SLawson/PMODIO/src/function_test/pmodio_function_test.xdc

## Constraints file for the PMODIO Function Test
## 

## Clock signal
set_property -dict { PACKAGE_PIN E3    IOSTANDARD LVCMOS33 } [get_ports { clk }]; #IO_L12P_T1_MRCC_35 Sch=clk100mhz
create_clock -add -name sys_clk_pin -period 10.00 -waveform {0 5} [get_ports {clk}];

## LEDs

set_property -dict { PACKAGE_PIN H17   IOSTANDARD LVCMOS33 } [get_ports { led[0] }]; #IO_L18P_T2_A24_15 Sch=led[0]
set_property -dict { PACKAGE_PIN K15   IOSTANDARD LVCMOS33 } [get_ports { led[1] }]; #IO_L24P_T3_RS1_15 Sch=led[1]
set_property -dict { PACKAGE_PIN J13   IOSTANDARD LVCMOS33 } [get_ports { led[2] }]; #IO_L17N_T2_A25_15 Sch=led[2]
set_property -dict { PACKAGE_PIN N14   IOSTANDARD LVCMOS33 } [get_ports { led[3] }]; #IO_L8P_T1_D11_14 Sch=led[3]
set_property -dict { PACKAGE_PIN R18   IOSTANDARD LVCMOS33 } [get_ports { led[4] }]; #IO_L7P_T1_D09_14 Sch=led[4]
set_property -dict { PACKAGE_PIN V17   IOSTANDARD LVCMOS33 } [get_ports { led[5] }]; #IO_L18N_T2_A11_D27_14 Sch=led[5]
set_property -dict { PACKAGE_PIN U17   IOSTANDARD LVCMOS33 } [get_ports { led[6] }]; #IO_L17P_T2_A14_D30_14 Sch=led[6]
set_property -dict { PACKAGE_PIN U16   IOSTANDARD LVCMOS33 } [get_ports { led[7] }]; #IO_L18P_T2_A12_D28_14 Sch=led[7]
set_property -dict { PACKAGE_PIN V16   IOSTANDARD LVCMOS33 } [get_ports { led[8] }]; #IO_L16N_T2_A15_D31_14 Sch=led[8]
set_property -dict { PACKAGE_PIN T15   IOSTANDARD LVCMOS33 } [get_ports { led[9] }]; #IO_L14N_T2_SRCC_14 Sch=led[9]
set_property -dict { PACKAGE_PIN U14   IOSTANDARD LVCMOS33 } [get_ports { led[10] }]; #IO_L22P_T3_A05_D21_14 Sch=led[10]
set_property -dict { PACKAGE_PIN T16   IOSTANDARD LVCMOS33 } [get_ports { led[11] }]; #IO_L15N_T2_DQS_DOUT_CSO_B_14 Sch=led[11]
set_property -dict { PACKAGE_PIN V15   IOSTANDARD LVCMOS33 } [get_ports { led[12] }]; #IO_L16P_T2_CSI_B_14 Sch=led[12]
set_property -dict { PACKAGE_PIN V14   IOSTANDARD LVCMOS33 } [get_ports { led[13] }]; #IO_L22N_T3_A04_D20_14 Sch=led[13]
set_property -dict { PACKAGE_PIN V12   IOSTANDARD LVCMOS33 } [get_ports { led[14] }]; #IO_L20N_T3_A07_D23_14 Sch=led[14]
set_property -dict { PACKAGE_PIN V11   IOSTANDARD LVCMOS33 } [get_ports { led[15] }]; #IO_L21N_T3_DQS_A06_D22_14 Sch=led[15]

##Buttons

set_property -dict { PACKAGE_PIN C12   IOSTANDARD LVCMOS33 } [get_ports { reset_n }]; #IO_L3P_T0_DQS_AD1P_15 Sch=cpu_resetn

##Pmod Headers

## JA - LCD Data Bus

set_property -dict { PACKAGE_PIN C17   IOSTANDARD LVCMOS33 } [get_ports { lcd_en_op   }]; #IO_L20N_T3_A19_15 Sch=ja[1]
set_property -dict { PACKAGE_PIN D18   IOSTANDARD LVCMOS33 } [get_ports { lcd_reset_n }]; #IO_L21N_T3_DQS_A18_15 Sch=ja[2]
set_property -dict { PACKAGE_PIN E18   IOSTANDARD LVCMOS33 } [get_ports { lcd_cs_1    }]; #IO_L21P_T3_DQS_15 Sch=ja[3]
set_property -dict { PACKAGE_PIN G17   IOSTANDARD LVCMOS33 } [get_ports { lcd_cs_2    }]; #IO_L18N_T2_A23_15 Sch=ja[4]
set_property -dict { PACKAGE_PIN D17   IOSTANDARD LVCMOS33 } [get_ports { lcd_reg_sel }]; #IO_L16N_T2_A27_15 Sch=ja[7]
set_property -dict { PACKAGE_PIN E17   IOSTANDARD LVCMOS33 } [get_ports { rotary_btn  }]; #IO_L16P_T2_A28_15 Sch=ja[8]
set_property -dict { PACKAGE_PIN F18   IOSTANDARD LVCMOS33 } [get_ports { rotary_b    }]; #IO_L22N_T3_A16_15 Sch=ja[9]
set_property -dict { PACKAGE_PIN G18   IOSTANDARD LVCMOS33 } [get_ports { rotary_a    }]; #IO_L22P_T3_A17_15 Sch=ja[10]


## JB - LCD Control Bus & Rotary Encoder Bus

set_property -dict { PACKAGE_PIN D14   IOSTANDARD LVCMOS33 } [get_ports { lcd_data[7] }]; #IO_L1P_T0_AD0P_15 Sch=jb[1]
set_property -dict { PACKAGE_PIN F16   IOSTANDARD LVCMOS33 } [get_ports { lcd_data[5] }]; #IO_L14N_T2_SRCC_15 Sch=jb[2]
set_property -dict { PACKAGE_PIN G16   IOSTANDARD LVCMOS33 } [get_ports { lcd_data[3] }]; #IO_L13N_T2_MRCC_15 Sch=jb[3]
set_property -dict { PACKAGE_PIN H14   IOSTANDARD LVCMOS33 } [get_ports { lcd_data[1] }]; #IO_L15P_T2_DQS_15 Sch=jb[4]
set_property -dict { PACKAGE_PIN E16   IOSTANDARD LVCMOS33 } [get_ports { lcd_data[6] }]; #IO_L11N_T1_SRCC_15 Sch=jb[7]
set_property -dict { PACKAGE_PIN F13   IOSTANDARD LVCMOS33 } [get_ports { lcd_data[4] }]; #IO_L5P_T0_AD9P_15 Sch=jb[8]
set_property -dict { PACKAGE_PIN G13   IOSTANDARD LVCMOS33 } [get_ports { lcd_data[2] }]; #IO_0_15 Sch=jb[9]
set_property -dict { PACKAGE_PIN H16   IOSTANDARD LVCMOS33 } [get_ports { lcd_data[0] }]; #IO_L13P_T2_MRCC_15 Sch=jb[10]
